KLC81/calcreactorx-esp32/include/secrets.example.h

#pragma once

#define WIFI_SSID "your-wifi-name"
#define WIFI_PASSWORD "your-wifi-password"

#define WIFI_AP_SSID "AquaPH-Controller"
#define WIFI_AP_PASSWORD "aquaph1234"

#define WIFI_OTA_PASSWORD "aquaph1234"
